mike-rankin/ESP32-S3_CO2_Monitor/Images/Plugged_In.jpg

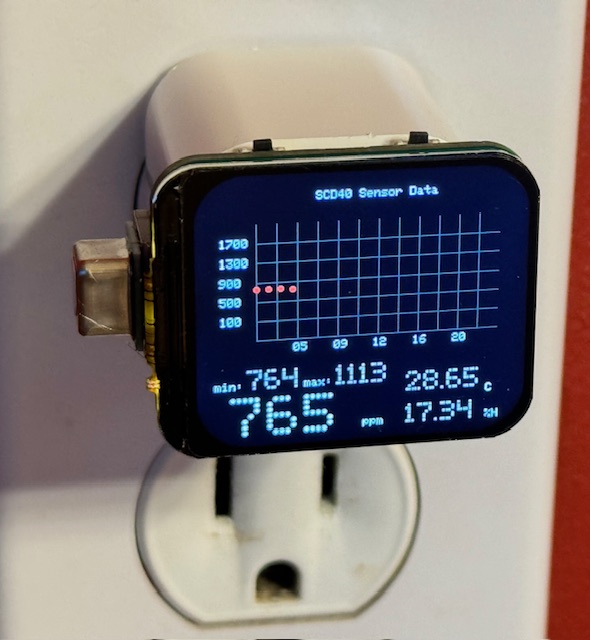
Images/Plugged_In.jpg
