mike-rankin/ESP32-S3_CO2_Monitor/Images/Rev4.png

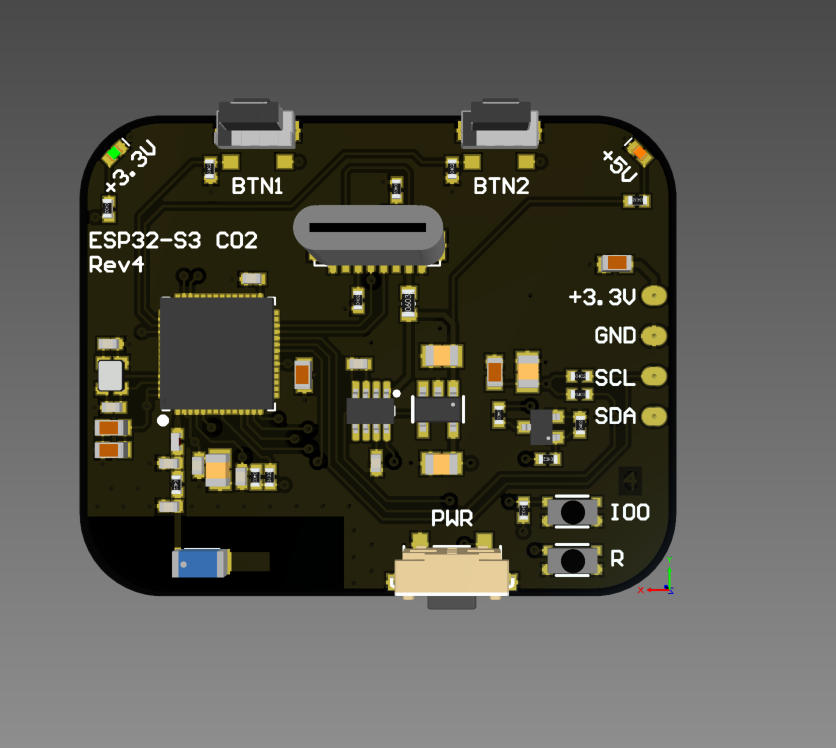
Images/Rev4.png
