mike-rankin/ESP32-S3_CO2_Monitor/Images/Rev5_with_charger.jpg

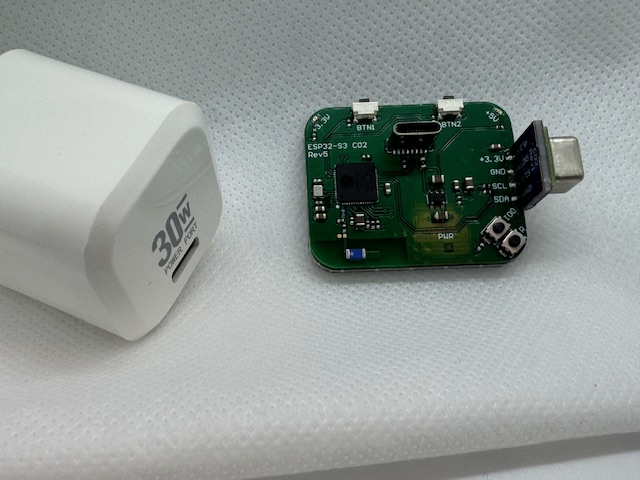
Images/Rev5_with_charger.jpg
