mike-rankin/ESP32-S3_CO2_Monitor/Images/stanoff_back.jpg

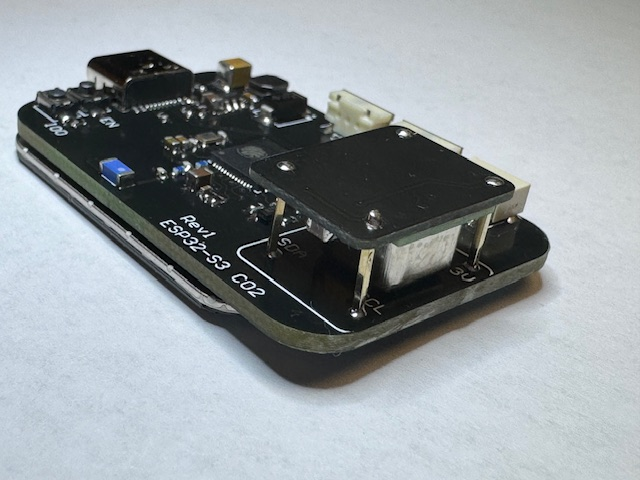
Images/stanoff_back.jpg
