mike-rankin/ESP32-S3_CO2_Monitor/Images/stanoff_data.jpg

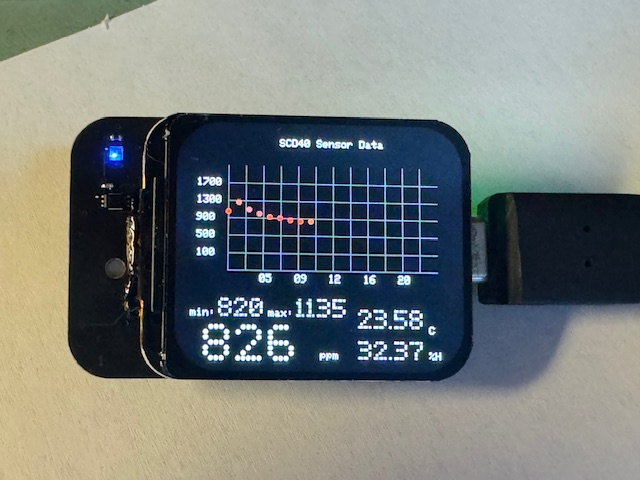
Images/stanoff_data.jpg
