mike-rankin/ESP32-S3_CO2_Monitor/Images/W_Charger.jpg

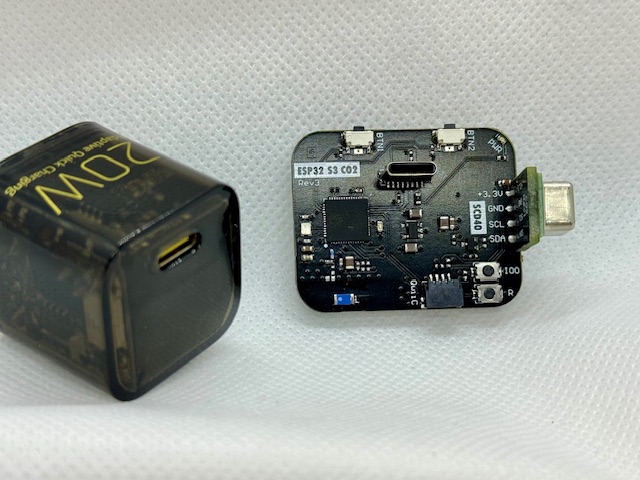
Images/W_Charger.jpg
